sfeister/sidekick-sc22/CAD/STL/Target Hat.stl

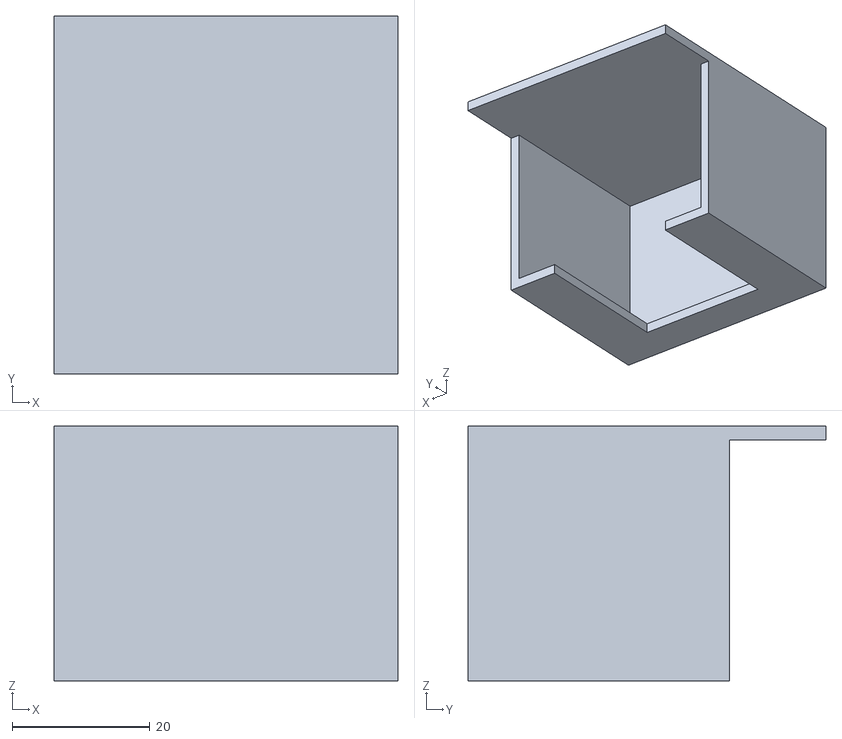
[picture p15: CAD file, 2023-03-24]
CAD/STL/Target Hat.stl
50.0 x 52.0 x 37.0
