sfeister/sidekick-sc22/Python/debug-ioc/demo1.py

from picamera2 import Picamera2, Preview
import time

from picamera2.controls import Controls

picam2 = Picamera2()
picam2.start_preview(Preview.QTGL)

preview_config = picam2.create_preview_configuration()
picam2.configure(preview_config)

picam2.start()
time.sleep(1)

ctrls = Controls(picam2)
ctrls.AnalogueGain = 1.0
ctrls.ExposureTime = 10000
picam2.set_controls(ctrls)

time.sleep(100)
